PedPEx/SinCosEnc-Conv_EP5101/pics/concept_DIN-rail/0_Beckhoff_EP5101_v4_5.png

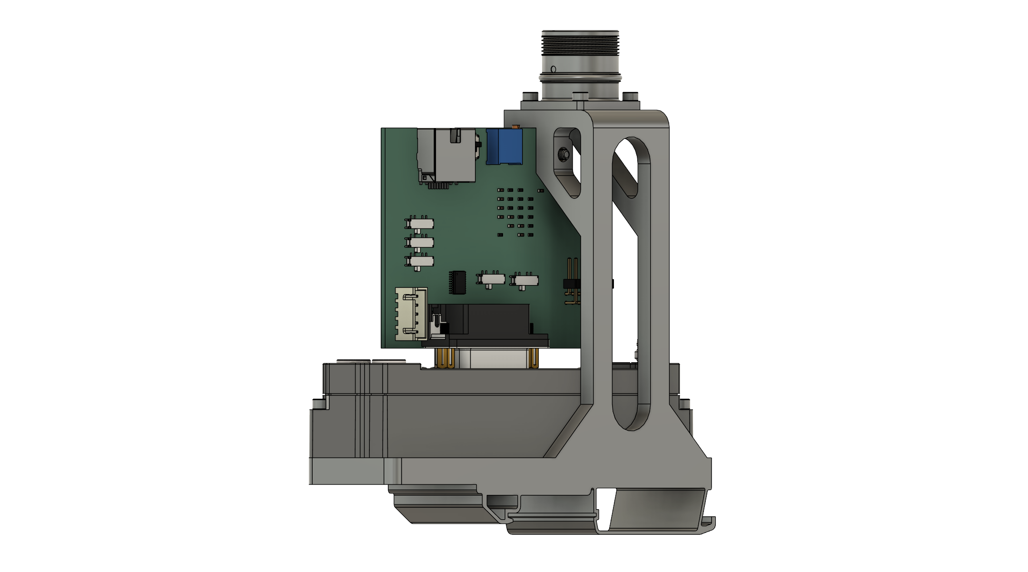
pics/concept_DIN-rail/0_Beckhoff_EP5101_v4_5.png
