PedPEx/SinCosEnc-Conv_EP5101/pics/concept_DIN-rail/0_Gesamt_DinRail02_v1_1.png

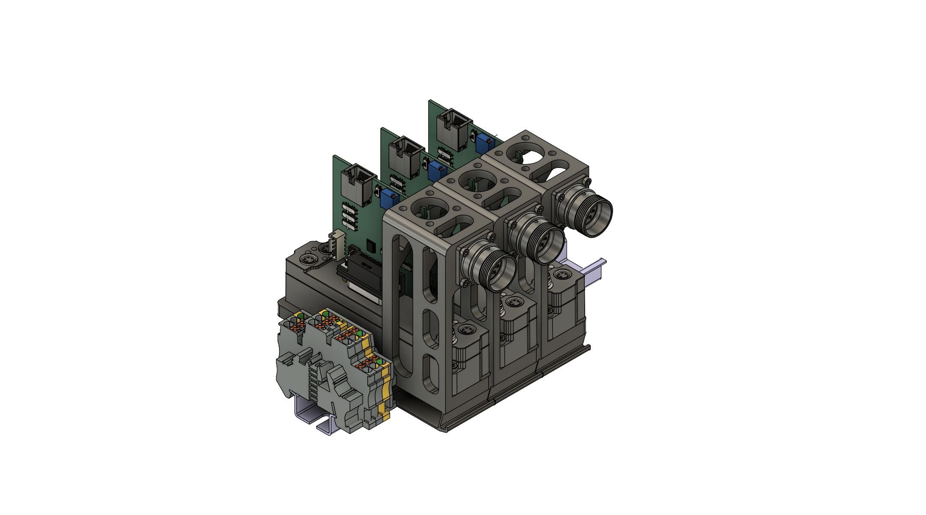
pics/concept_DIN-rail/0_Gesamt_DinRail02_v1_1.png
