PedPEx/SinCosEnc-Conv_EP5101/pics/concept_DIN-rail/1_Gesamt_DinRail_v2_1.png

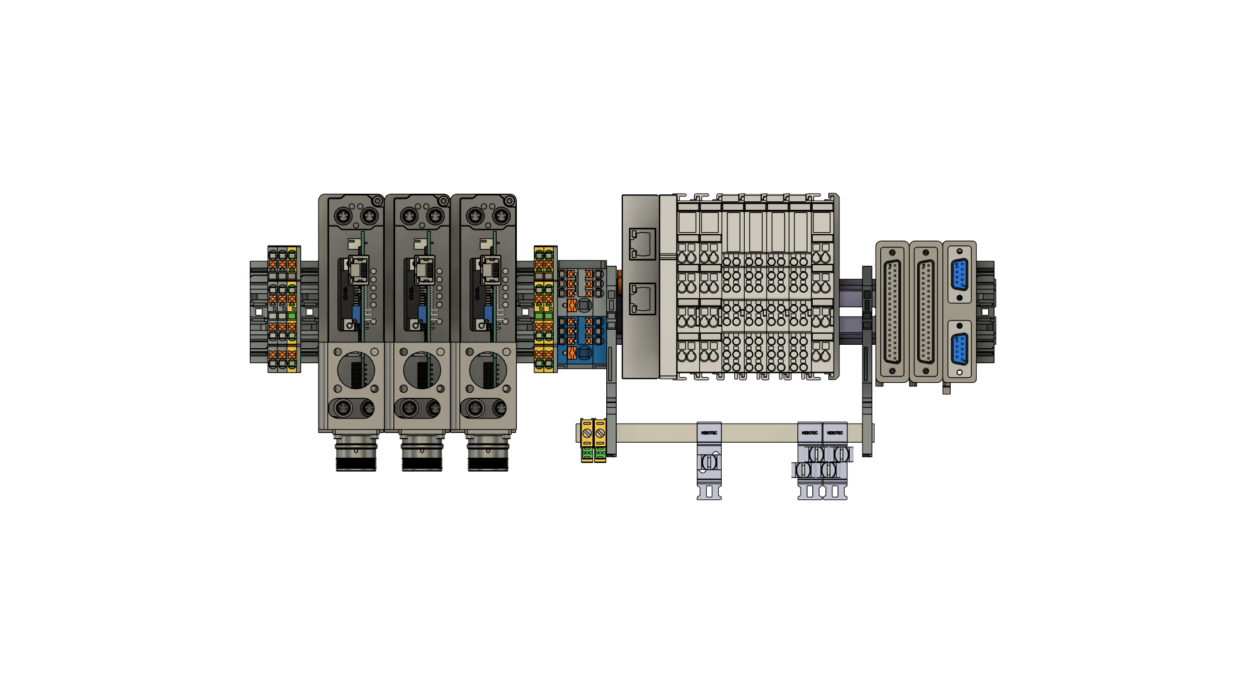
pics/concept_DIN-rail/1_Gesamt_DinRail_v2_1.png
