PedPEx/SinCosEnc-Conv_EP5101/pics/concept_DIN-rail/EP5101-0011_DinRail_CON-downside_v4_3.png

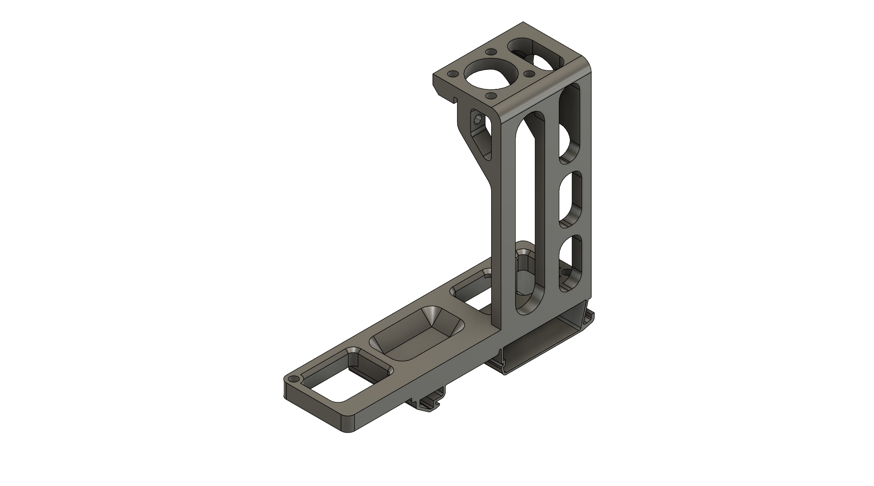
pics/concept_DIN-rail/EP5101-0011_DinRail_CON-downside_v4_3.png
