PedPEx/SinCosEnc-Conv_EP5101/pics/PCB_render/v093.png

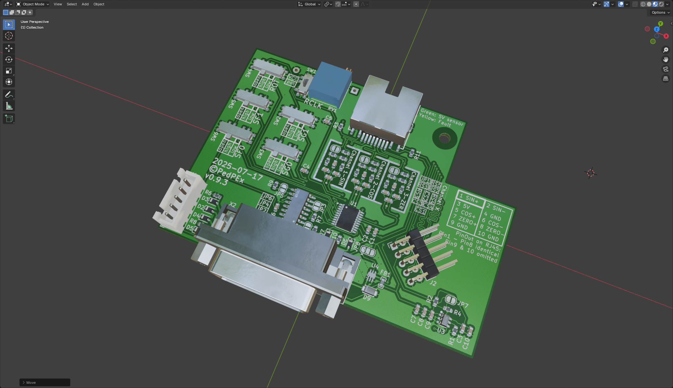
pics/PCB_render/v093.png
