PedPEx/SinCosEnc-Conv_EP5101/pics/PCB_render/v093_3.png

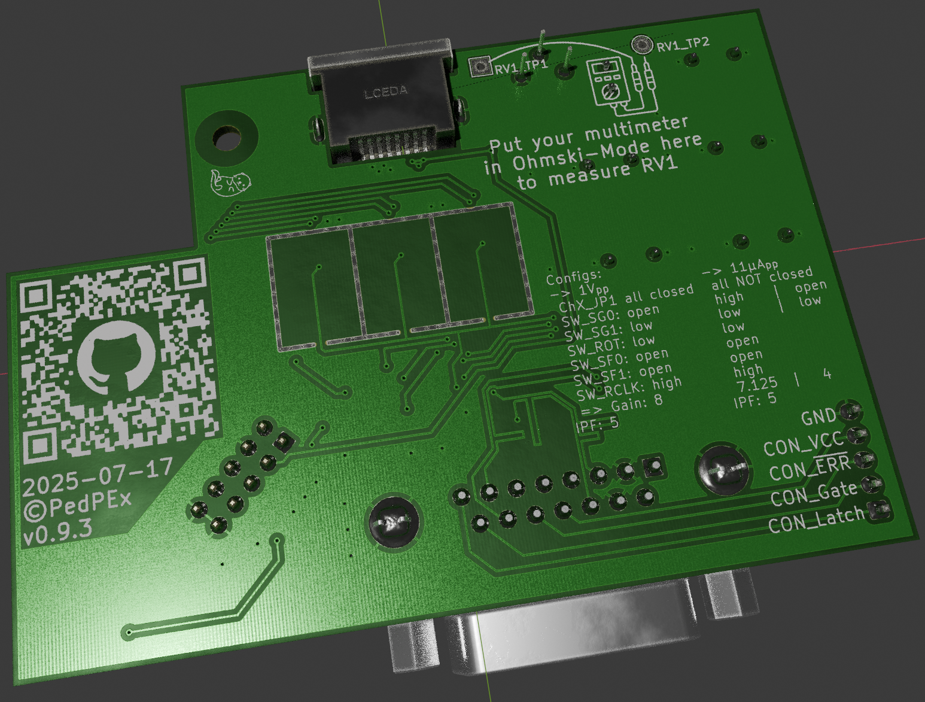
pics/PCB_render/v093_3.png
