PedPEx/SinCosEnc-Conv_EP5101/pics/used_on_PCB/21649597-multimetersymbol-vektor.jpg

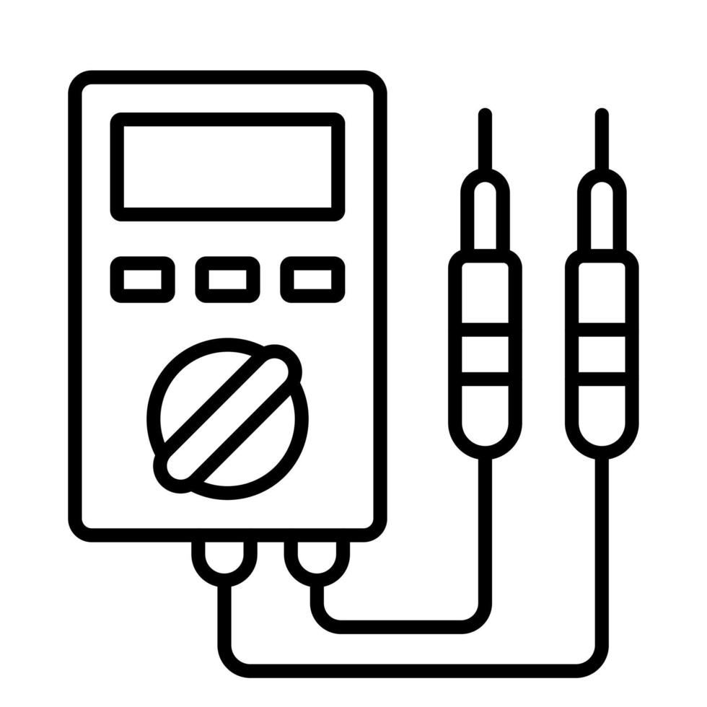
pics/used_on_PCB/21649597-multimetersymbol-vektor.jpg
